rodan/ampy/hardware/ltspice/snd_detect.asc

C1: cap; 470n
C2: cap; 100n
C3: cap; 1n
C4: cap; 1µ
C5: cap; 1n
C6: cap; 100n
D1: diode; 1N4148
D2: diode; 1N4148
D3: diode; 1N4148
M1: nmos; IRLML6246
R1: res; 1K
R2: res; 47K
R3: res; 4Meg7
R4: res; 4Meg7
R5: res; 47K
R6: res; 47K
R7: res; 10K
R8: res; 47K
R9: res; 4Meg7
R10: res; 100K
R11: res; 1K
R12: res; 10K
R13: res; 680
U2: UniversalOpamp2
U3: LT1017
V1: VOLTAGE; 3V3
V2: voltage; ""; AC 1
V4: voltage; SINE(0 0.005 1K)
Named nets: 0, 3V3, IN, comp, ref, sig, amp, out
;tran 0 160m 150m
.ac dec 20 1 1000k
.op
