rodan/ampy/hardware/ltspice/mixer.asc

C1: cap; 1n
C2: cap; 1µ
C3: cap; 1n
C4: cap; 1µ
R1: res; 100K
R2: res; 1K
R3: res; 100K
R4: res; 0.001R
R5: res; 4K7
R6: res; 10K
R7: res; 10K
R8: res; 0.001R
R9: res; 10K
R10: res; 100K
R11: res; 1K
R12: res; 100K
R13: res; 4K7
R14: res; 10K
R15: res; 10K
U1: UniversalOpamp2
U2: UniversalOpamp2
U3: UniversalOpamp2
U4: UniversalOpamp2
V1: VOLTAGE; 5V
V2: voltage; ""; AC 1
V3: VOLTAGE; 5V
V4: voltage; SINE(0 0.100 1K)
V5: VOLTAGE; 15V
V6: VOLTAGE; 15V
V7: voltage; SINE(0 0.100 1K)
V8: voltage; ""; AC 1
Named nets: 0, +5V, -5V, +15V, -15V
.tran 0 260m 250m
;ac dec 20 1 100k
.op
