rodan/ampy/firmware_brain/config.h

#ifndef _CONFIG_H_
#define _CONFIG_H_

//#define USE_UART
#define USE_WATCHDOG
//#define CONFIG_DEBUG

//#define HARDWARE_I2C

////////////////////////////////////////
//
// stop changing anything beyond this point
//

#ifndef USE_UART
    #define USE_I2C
#endif

#endif
