rodan/ampy/firmware_brain/drivers/i2c.h

/*
* Copyright (c) 2013, Alexander I. Mykyta
* All rights reserved.
* 
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
* THIS SOFTWARE IS PROVIDED BY THE COPYRIGHT HOLDERS AND CONTRIBUTORS "AS IS" AND
* ANY EXPRESS OR IMPLIED WARRANTIES, INCLUDING, BUT NOT LIMITED TO, THE IMPLIED
* WARRANTIES OF MERCHANTABILITY AND FITNESS FOR A PARTICULAR PURPOSE ARE
* DISCLAIMED. IN NO EVENT SHALL THE COPYRIGHT OWNER OR CONTRIBUTORS BE LIABLE FOR
* ANY DIRECT, INDIRECT, INCIDENTAL, SPECIAL, EXEMPLARY, OR CONSEQUENTIAL DAMAGES
* (INCLUDING, BUT NOT LIMITED TO, PROCUREMENT OF SUBSTITUTE GOODS OR SERVICES;
* LOSS OF USE, DATA, OR PROFITS; OR BUSINESS INTERRUPTION) HOWEVER CAUSED AND
* ON ANY THEORY OF LIABILITY, WHETHER IN CONTRACT, STRICT LIABILITY, OR TORT
* (INCLUDING NEGLIGENCE OR OTHERWISE) ARISING IN ANY WAY OUT OF THE USE OF THIS
* SOFTWARE, EVEN IF ADVISED OF THE POSSIBILITY OF SUCH DAMAGE.
*/

/**
* \addtogroup MOD_I2C I2C Bus
* \brief Application-level I2C master driver.
* \author Alex Mykyta 
*
* 
* ### MSP430 Processor Families Supported: ###
*   Family  | Supported
*   ------- | ----------
*   1xx     | -
*   2xx     | -
*   4xx     | -
*   5xx     | Yes
*   6xx     | Yes
* 
* \{
**/

/**
* \file
* \brief Include file for \ref MOD_I2C
* \author Alex Mykyta 
**/

#ifndef _I2C_H_
#define _I2C_H_

#ifdef __cplusplus
extern "C" {
#endif

#include <stdint.h>
#include <stdbool.h>

/*
#define I2C_TX_BUFF_LEN     8
uint8_t i2c_tx_buff[I2C_TX_BUFF_LEN];
*/

typedef struct {
    uint8_t slave_addr;     ///< Chip address of slave device
    uint8_t addr[3];        ///< register/command payload
    uint8_t addr_len;       ///< Number of addr bytes to use (1-3)
    uint8_t *data;          ///< Pointer to data transfer buffer
    uint16_t data_len;      ///< Number of bytes to transfer
    bool read;              ///< Indicates if the transfer is a read operation or not.
} i2c_package_t;

i2c_package_t pkg;

typedef enum {
    I2C_IDLE,               ///< Bus is idle. Ready for new transfer.
    I2C_BUSY,               ///< A transfer is in progress.
    I2C_FAILED              ///< Previous transfer failed. Ready for new transfer.
} i2c_status_t;

/**
 * \brief Initialize the I2C master module
 **/
    void i2c_init(void);

/**
 * \brief Uninitialize the I2C master module
 **/
    void i2c_uninit(void);

/**
 * \brief Start an I2C transfer
 * 
 * This function begins a new I2C transaction as described by the \c pkg struct. This function
 * is nonblocking and returns immediately after the transfer is started. The status of the transfer 
 * can be polled using the i2c_transfer_status() function. Alternatively, a \c callback function can
 * be executed when the transfer completes.
 * 
 * \note Global interrupts must be enabled.
 * 
 * \param pkg        Pointer to a package struct that describes the transfer operation.
 * \param callback   Optional pointer to a callback function to execute once the transfer completes
 *                   or fails. A NULL pointer disables the callback.
 **/
    void i2c_transfer_start(const i2c_package_t * pkg,
                            void (*callback) (i2c_status_t result));

/**
 * \brief Get the status of the I2C module
 * \return status of the bus.
 **/
    i2c_status_t i2c_transfer_status(void);

#ifdef __cplusplus
}
#endif
#endif
///\}
